JanelleW03/CEN3907-Blind-Spot-Helmet/RPTest/bat.py

from gpiozero import InputDevice, OutputDevice, PWMOutputDevice
from time import sleep, time

trig = OutputDevice(4)
echo = InputDevice(17)
motor = PWMOutputDevice(14)

sleep(2)

def get_pulse_time():
    trig.on()
    sleep(0.00001)
    trig.off()

    while echo.is_active == False:
        pulse_start = time()

    while echo.is_active == True:
        pulse_end = time()

    sleep(0.06)

    return pulse_end - pulse_start

##print(get_pulse_time())

def calculate_vibration(distance):
    vibration = (((distance - 0.02) * -1) / (4 - 0.02)) + 1
    return vibration

def calculate_distance(duration):
    speed = 343
    distance = speed * duration / 2
    return distance

while True:
    duration = get_pulse_time()
    distance = calculate_distance(duration)
    print(distance)
    vibration = calculate_vibration(distance)
    motor.value = vibration
