JanelleW03/CEN3907-Blind-Spot-Helmet/Camera/utils.py

"""
Utility functions to display the object detection results

Used for model testing and debugging; taken from https://github.com/BashMocha/object-detection-on-raspberry-pi
"""

import cv2
import numpy as np
from tflite_support.task import processor

_MARGIN = 10  # pixels
_ROW_SIZE = 10  # pixels
_FONT_SIZE = 1
_FONT_THICKNESS = 1
_TEXT_COLOR = (0, 0, 255)  # red


def visualize(
    image: np.ndarray,
    detection_result: processor.DetectionResult,
) -> np.ndarray:
    """Draws bounding boxes on the input image and return it.

    Args:
      image: The input RGB image.
      detection_result: The list of all "Detection" entities to be visualize.

    Returns:
      Image with bounding boxes.
    """
    for detection in detection_result.detections:
        # Draw bounding_box
        bbox = detection.bounding_box
        start_point = bbox.origin_x, bbox.origin_y
        end_point = bbox.origin_x + bbox.width, bbox.origin_y + bbox.height
        cv2.rectangle(image, start_point, end_point, _TEXT_COLOR, 3)

        # Draw label and score
        category = detection.categories[0]
        category_name = category.category_name
        probability = round(category.score, 2)
        result_text = category_name + ' (' + str(probability) + ')'
        text_location = (_MARGIN + bbox.origin_x,
                         _MARGIN + _ROW_SIZE + bbox.origin_y)
        cv2.putText(image, result_text, text_location, cv2.FONT_HERSHEY_PLAIN,
                    _FONT_SIZE, _TEXT_COLOR, _FONT_THICKNESS)

    return image
